4gymzogr/iot_project2024/Pictures/1_5_9dfddd3d-20bd-4d54-b8c2-3854cab92070.png

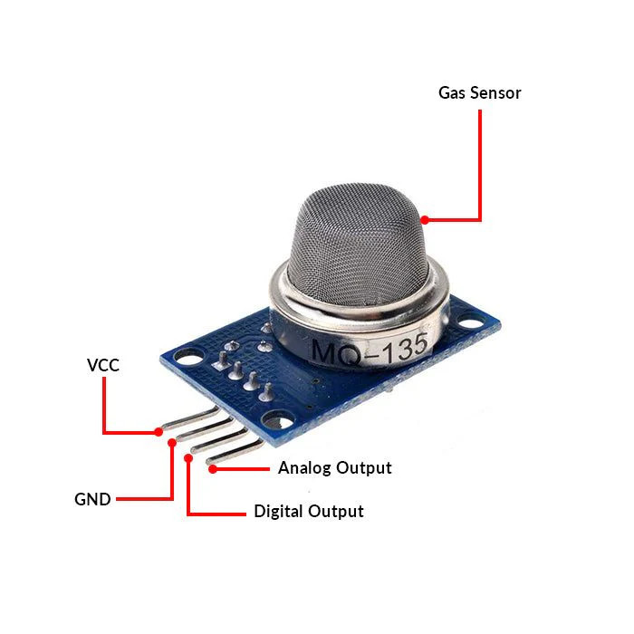
Pictures/1_5_9dfddd3d-20bd-4d54-b8c2-3854cab92070.png
