4gymzogr/iot_project2024/Pictures/1442273400_1452102046.jpg

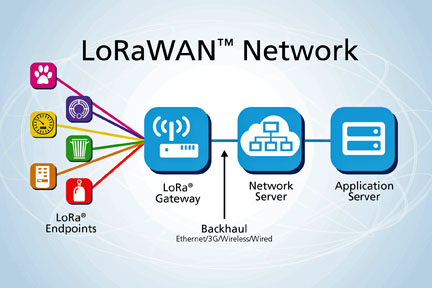
Pictures/1442273400_1452102046.jpg
