4gymzogr/iot_project2024/Pictures/arduino-uno-rev4-minima-dime.jpg

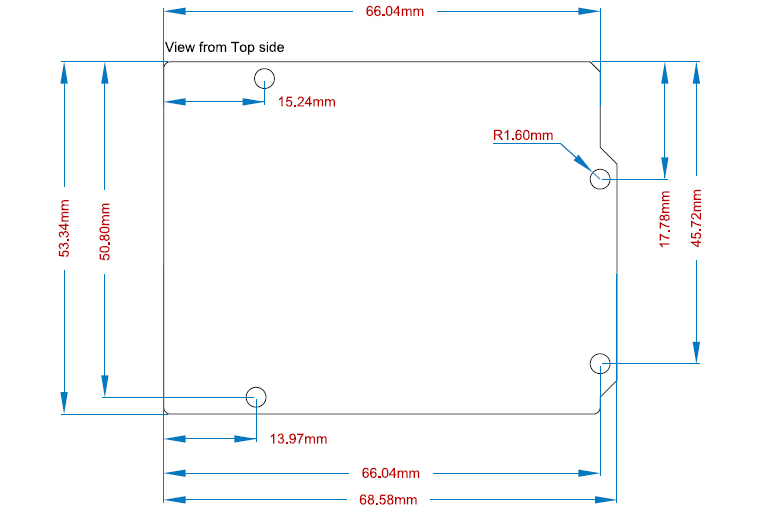
Pictures/arduino-uno-rev4-minima-dime.jpg
