4gymzogr/iot_project2024/Pictures/arduino_mega.png

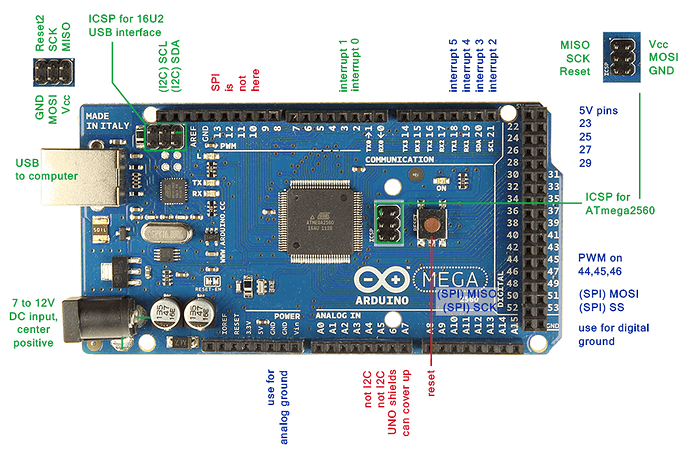
Pictures/arduino_mega.png
