4gymzogr/iot_project2024/Pictures/arduino_ubo.jpg

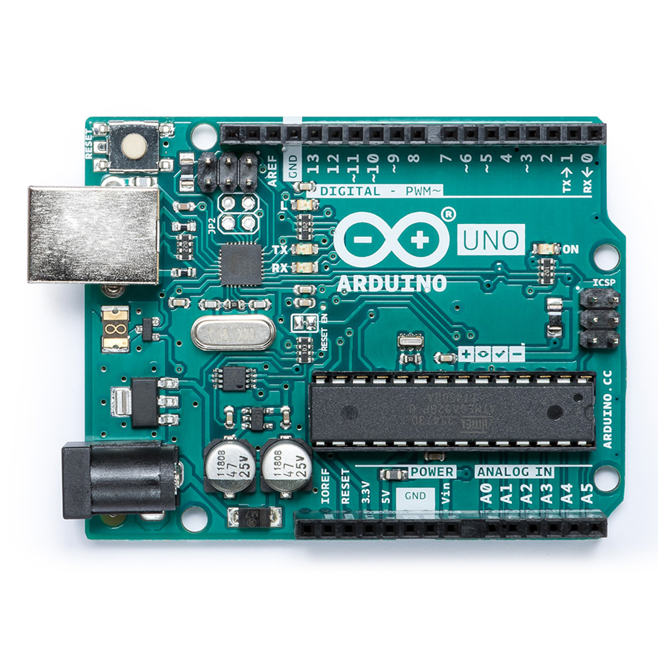
Pictures/arduino_ubo.jpg
