4gymzogr/iot_project2024/Pictures/BME688-Environmental-Sensor-with-Arduino-SPI-Connections.jpg

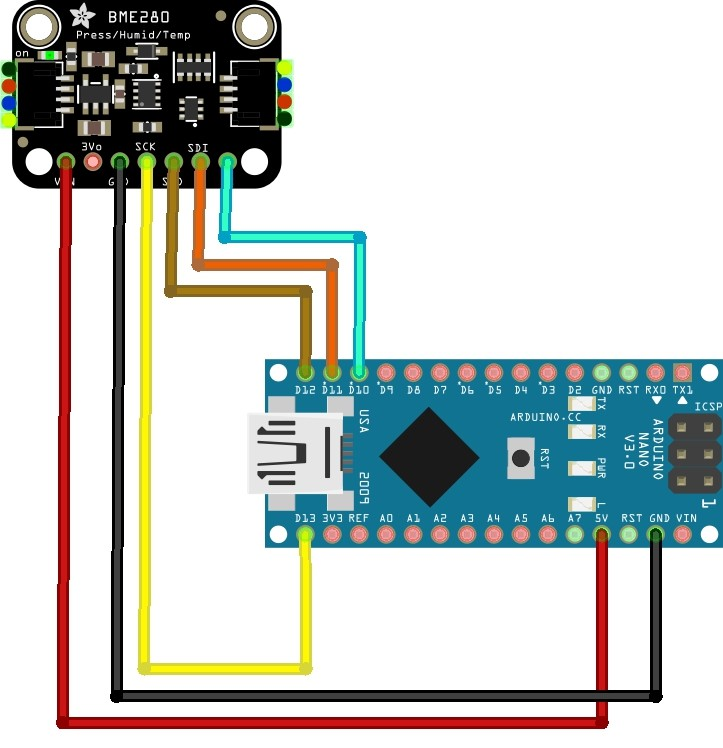
Pictures/BME688-Environmental-Sensor-with-Arduino-SPI-Connections.jpg
