4gymzogr/iot_project2024/Pictures/BME688-Temperature-Humidity-Pressure-and-Gas-Sensor-with-Arduino.jpg

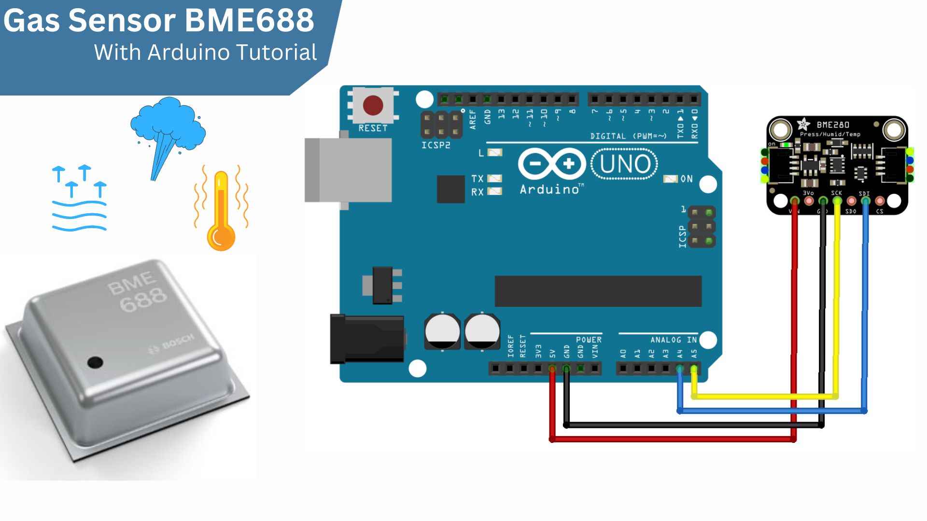
Pictures/BME688-Temperature-Humidity-Pressure-and-Gas-Sensor-with-Arduino.jpg
