4gymzogr/iot_project2024/Pictures/bme688.jpg

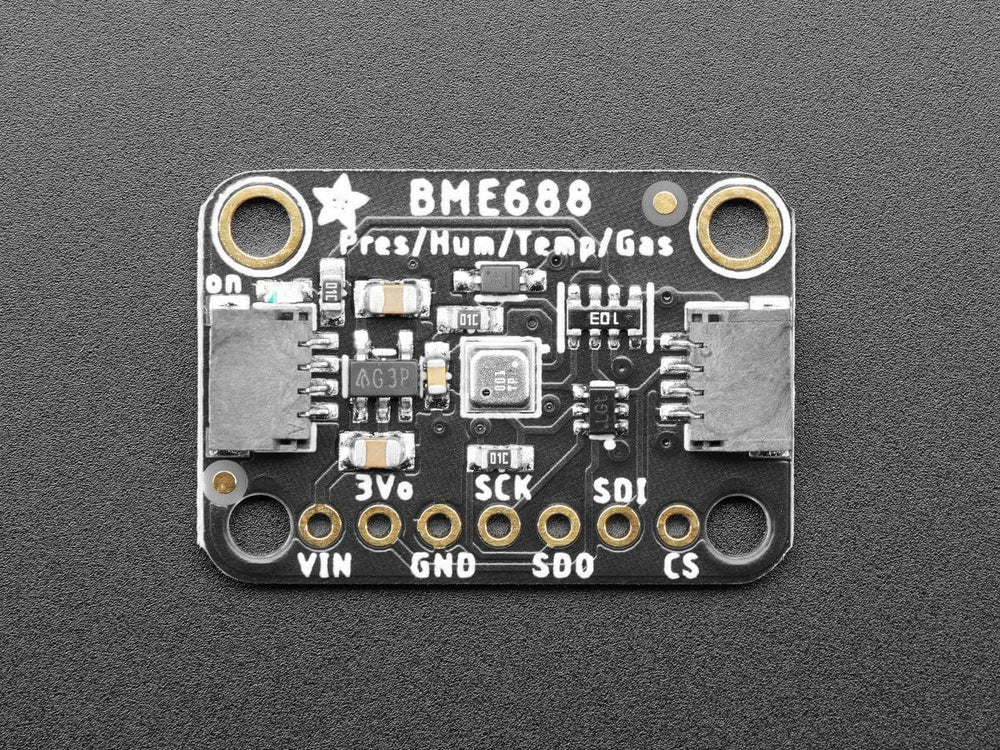
Pictures/bme688.jpg
