4gymzogr/iot_project2024/Pictures/indoor air quality.jpg

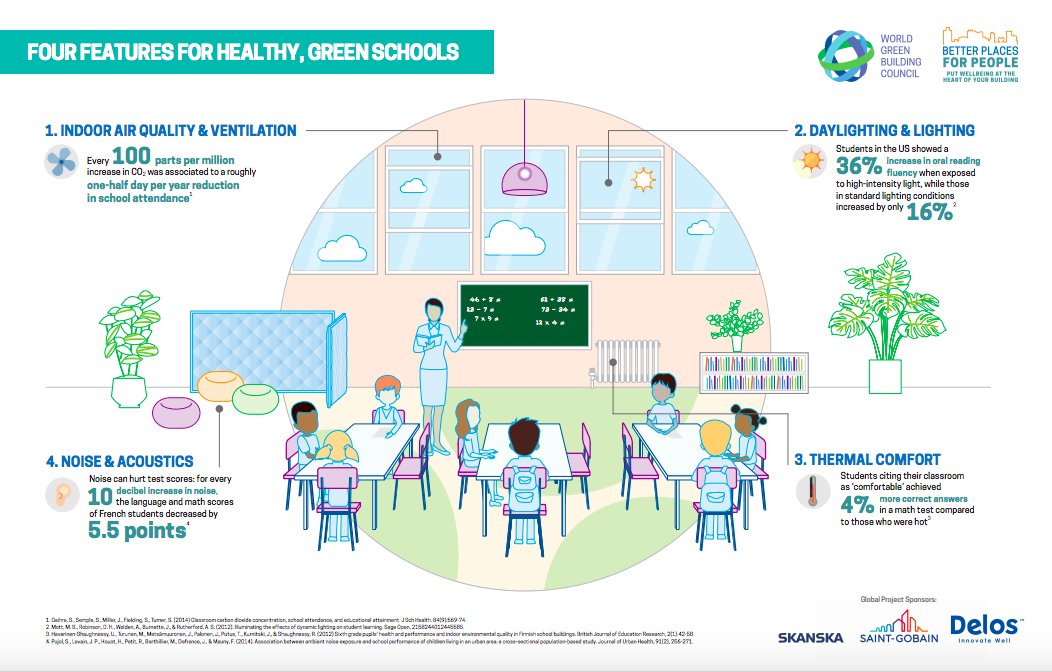
Pictures/indoor air quality.jpg
