4gymzogr/iot_project2024/Pictures/IoT1.png

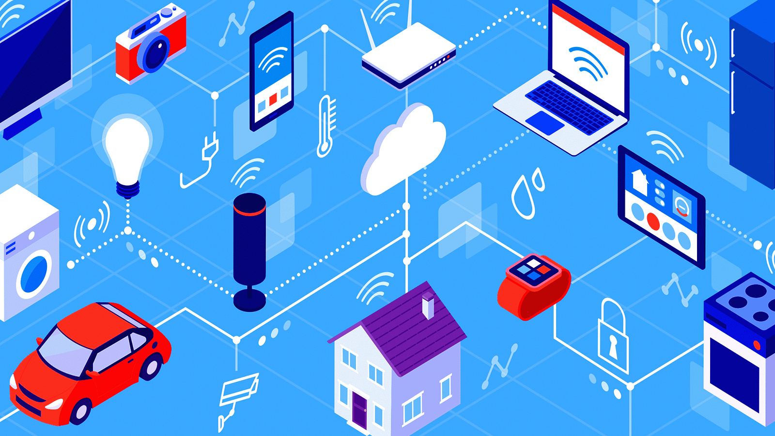
Pictures/IoT1.png
