4gymzogr/iot_project2024/Pictures/IoT2.jpg

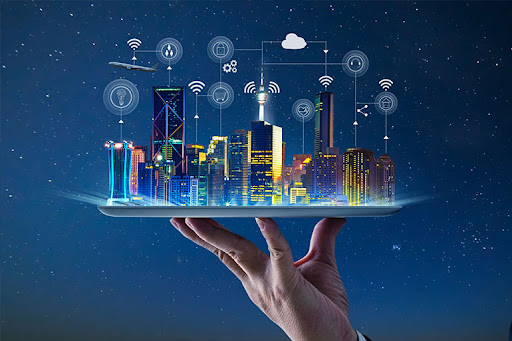
Pictures/IoT2.jpg
