4gymzogr/iot_project2024/Pictures/IoT3.png

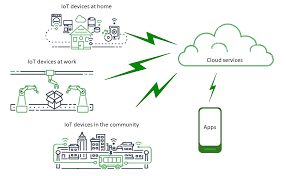
Pictures/IoT3.png
