4gymzogr/iot_project2024/Pictures/IoT4.jpg

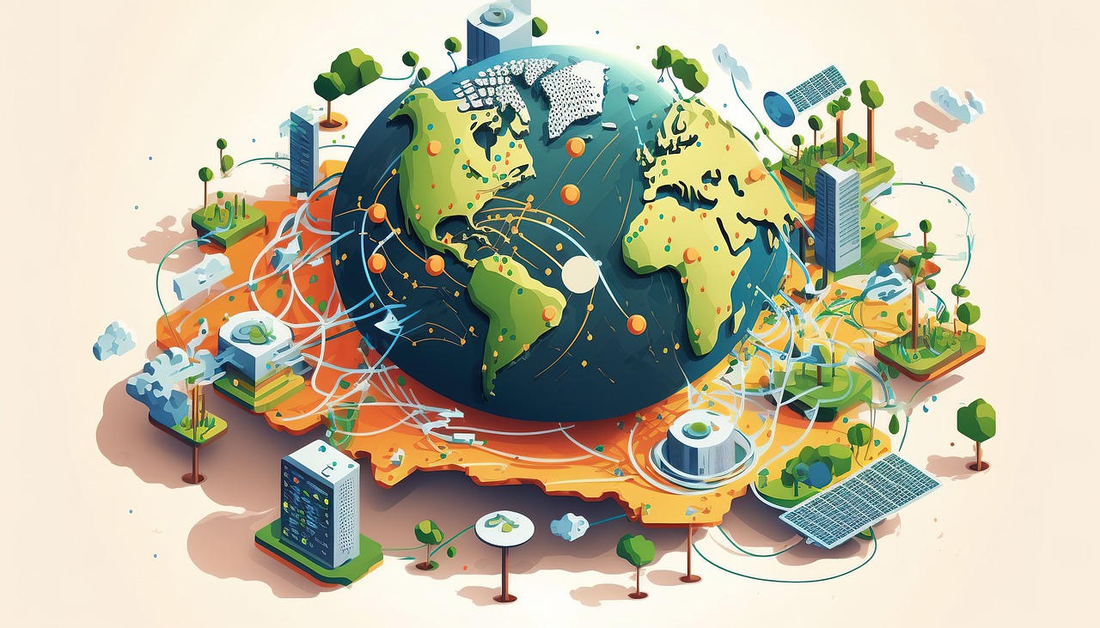
Pictures/IoT4.jpg
