4gymzogr/iot_project2024/Pictures/LDR-wire.jpg

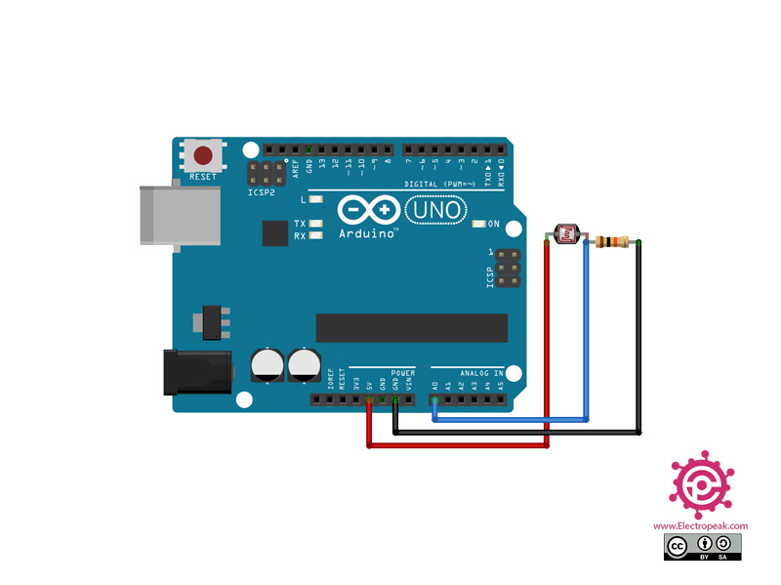
Pictures/LDR-wire.jpg
