4gymzogr/iot_project2024/Pictures/LDR-wire.png

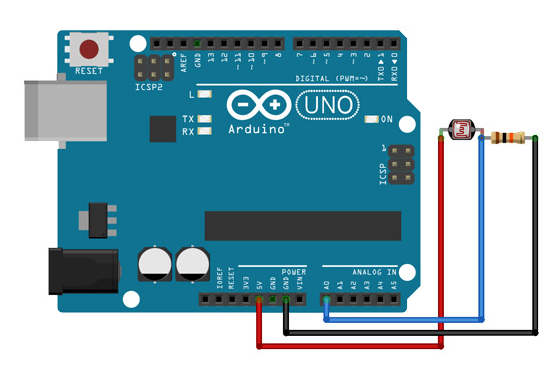
Pictures/LDR-wire.png
