4gymzogr/iot_project2024/Pictures/LDRsensor.jpg

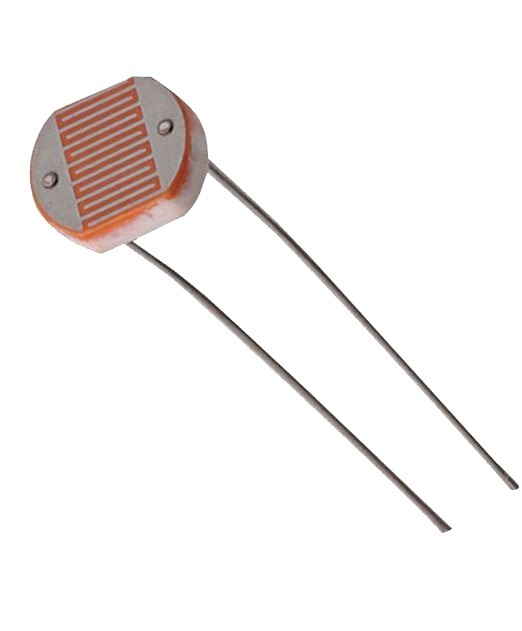
Pictures/LDRsensor.jpg
