4gymzogr/iot_project2024/Pictures/LoRa1.png

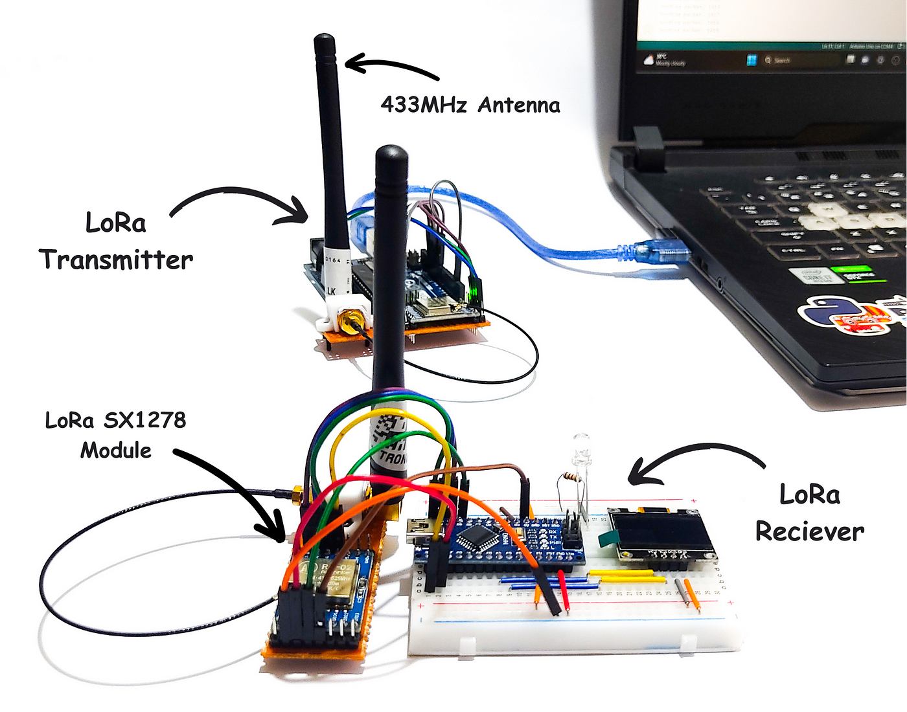
Pictures/LoRa1.png
