4gymzogr/iot_project2024/Pictures/lora-gateway-diagram.png

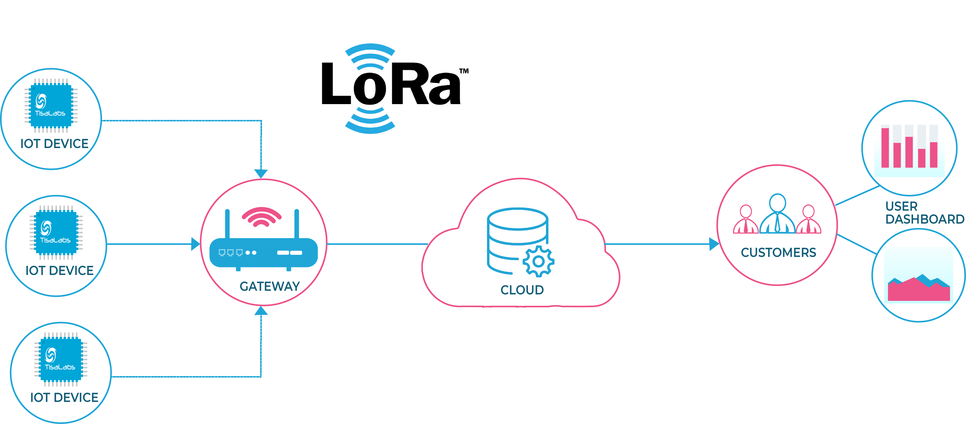
Pictures/lora-gateway-diagram.png
