4gymzogr/iot_project2024/Pictures/LoRa-rfm95w-868s2-3.jpeg

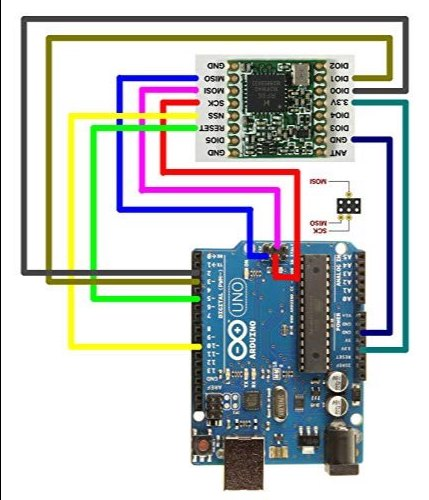
Pictures/LoRa-rfm95w-868s2-3.jpeg
