4gymzogr/iot_project2024/Pictures/LoRa-SX1278-with-Arduino-Nano.png.png

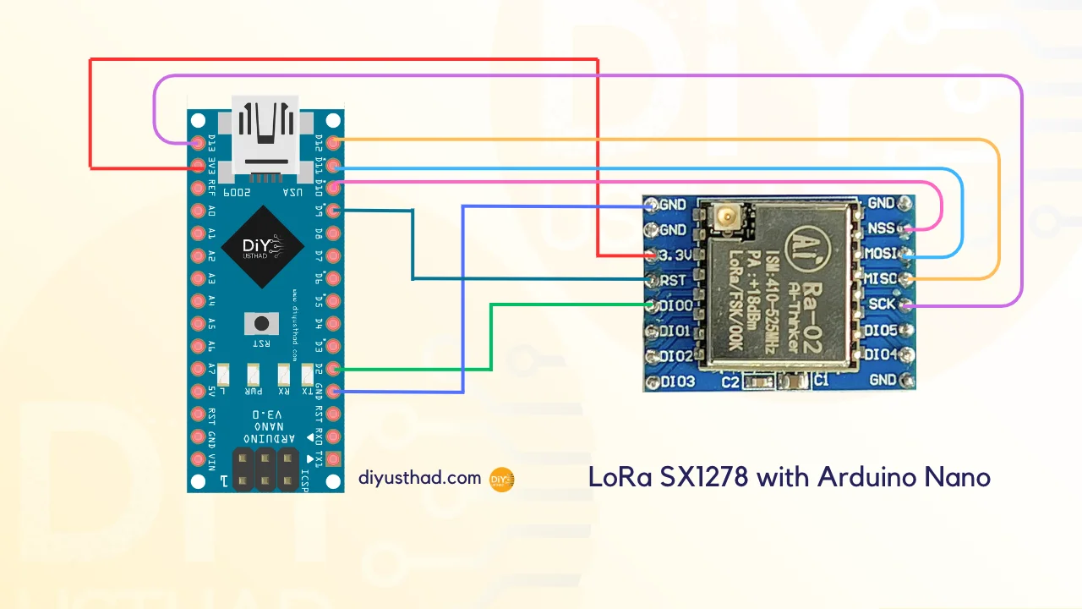
Pictures/LoRa-SX1278-with-Arduino-Nano.png.png
