4gymzogr/iot_project2024/Pictures/LoRa.jpg

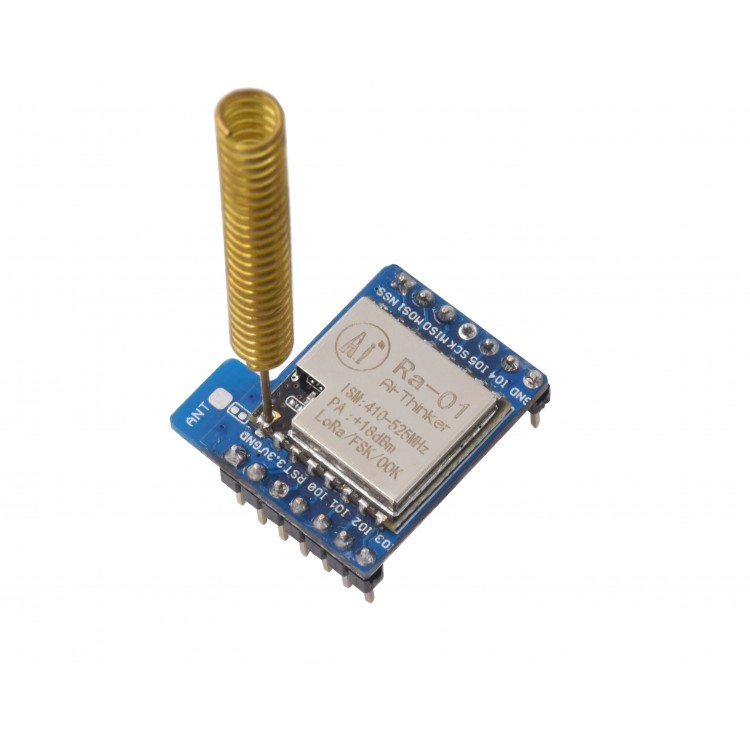
Pictures/LoRa.jpg
