4gymzogr/iot_project2024/Pictures/LoRaInArduinoUNO.jpg

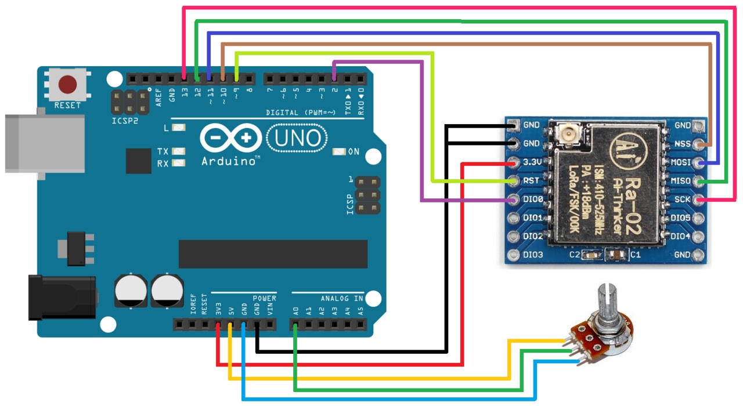
Pictures/LoRaInArduinoUNO.jpg
