4gymzogr/iot_project2024/Pictures/LoRaMQTTNetwork.jpg

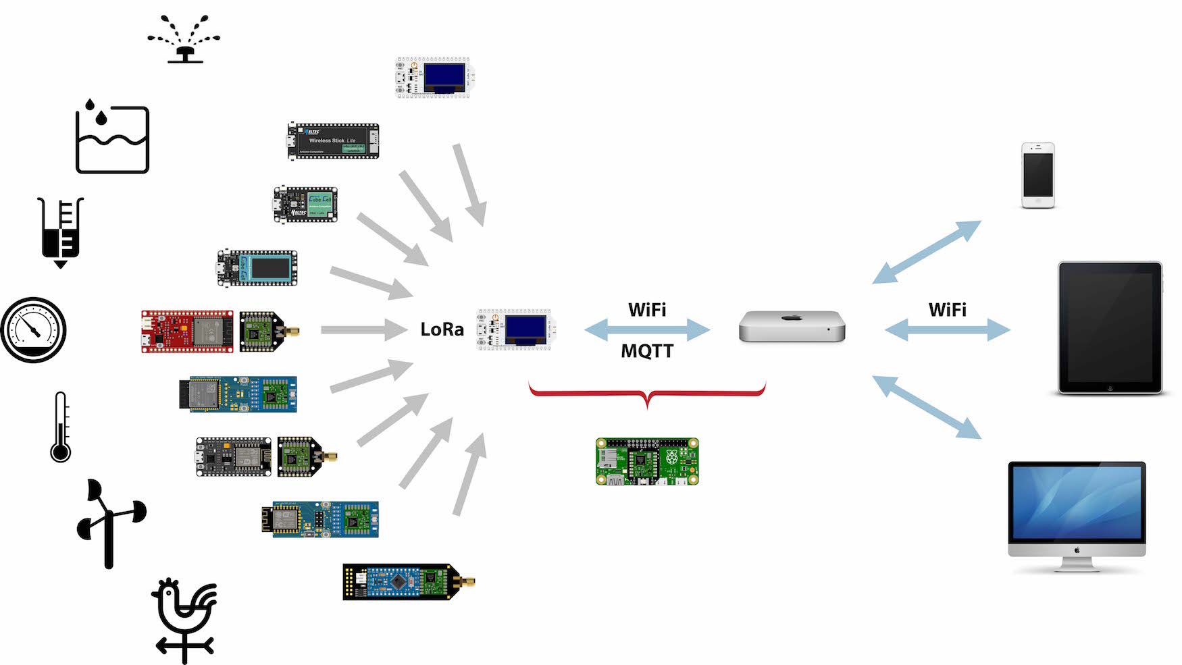
Pictures/LoRaMQTTNetwork.jpg
