4gymzogr/iot_project2024/Pictures/LoRaWAN-Network-Architecture.png

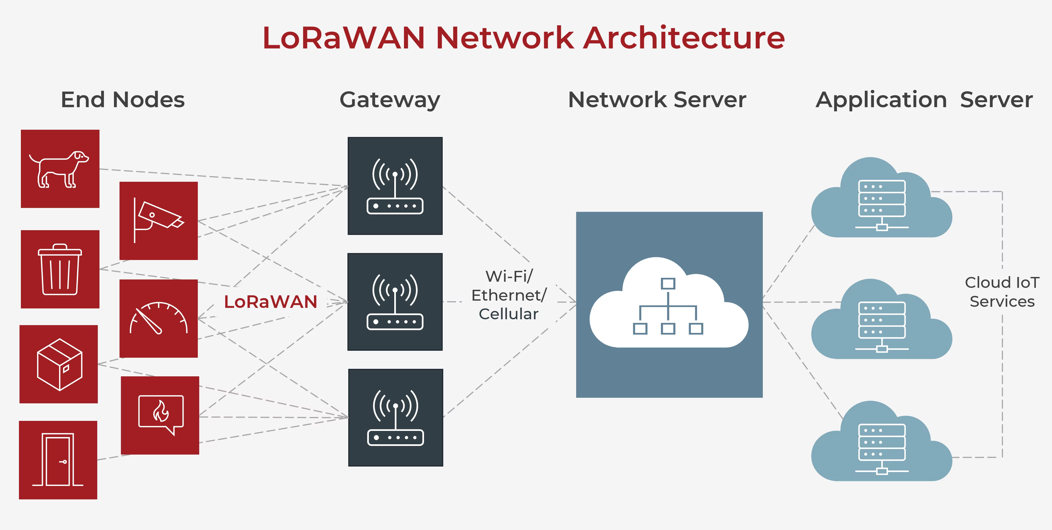
Pictures/LoRaWAN-Network-Architecture.png
