4gymzogr/iot_project2024/Pictures/MQ135-Load-Resistor-Location.png

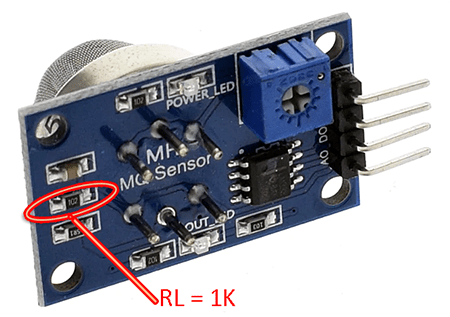
Pictures/MQ135-Load-Resistor-Location.png
