4gymzogr/iot_project2024/Pictures/MQ135.jpeg

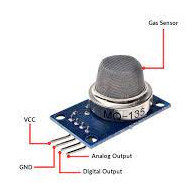
Pictures/MQ135.jpeg
