4gymzogr/iot_project2024/Pictures/MQ135_connect_with_arduino.jpeg

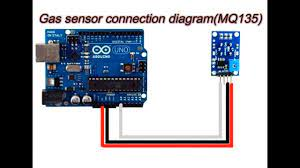
Pictures/MQ135_connect_with_arduino.jpeg
