4gymzogr/iot_project2024/Pictures/mqtt1.png

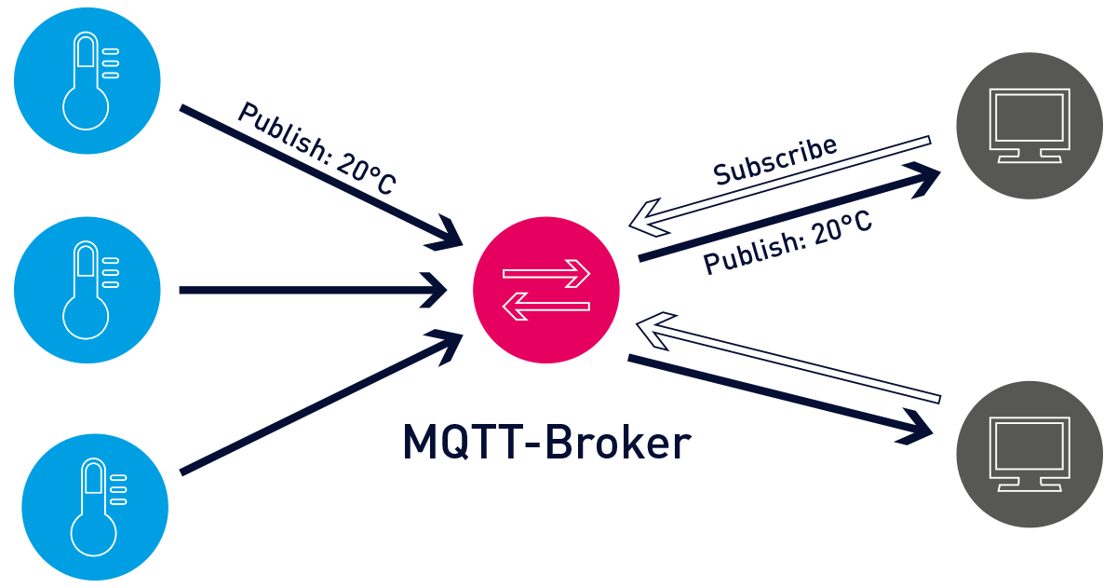
Pictures/mqtt1.png
