4gymzogr/iot_project2024/Pictures/MQTT2.jpg

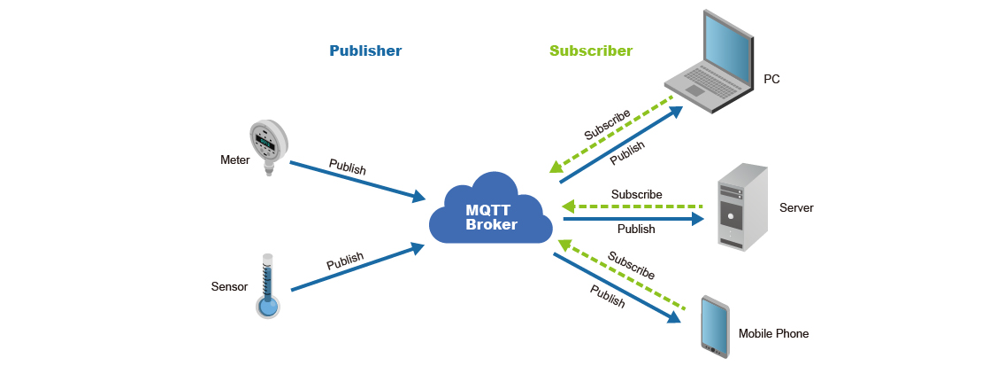
Pictures/MQTT2.jpg
