4gymzogr/iot_project2024/Pictures/OutlineDimensionsArduinoUNORev4WiFi.webp

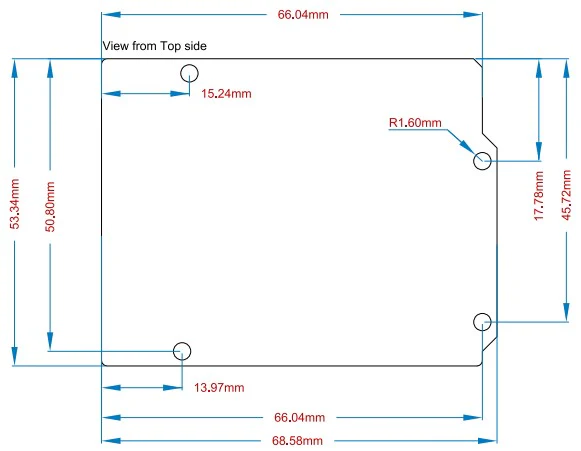
Pictures/OutlineDimensionsArduinoUNORev4WiFi.webp
