4gymzogr/iot_project2024/Pictures/rf001-rfm95w-868s2-2-1000x1000.jpeg

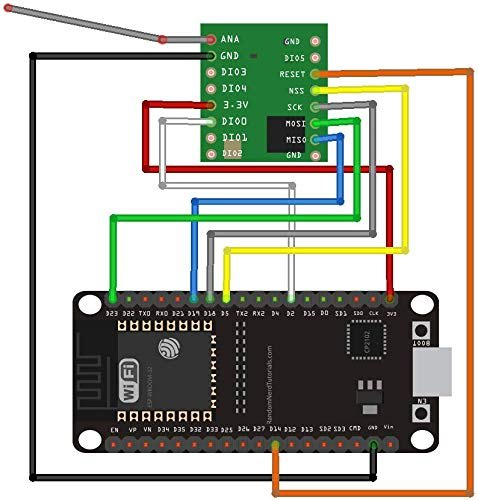
Pictures/rf001-rfm95w-868s2-2-1000x1000.jpeg
