4gymzogr/iot_project2024/Pictures/RoboticsTeamPhotos/IMG_20240421_123717820_HDR.jpg

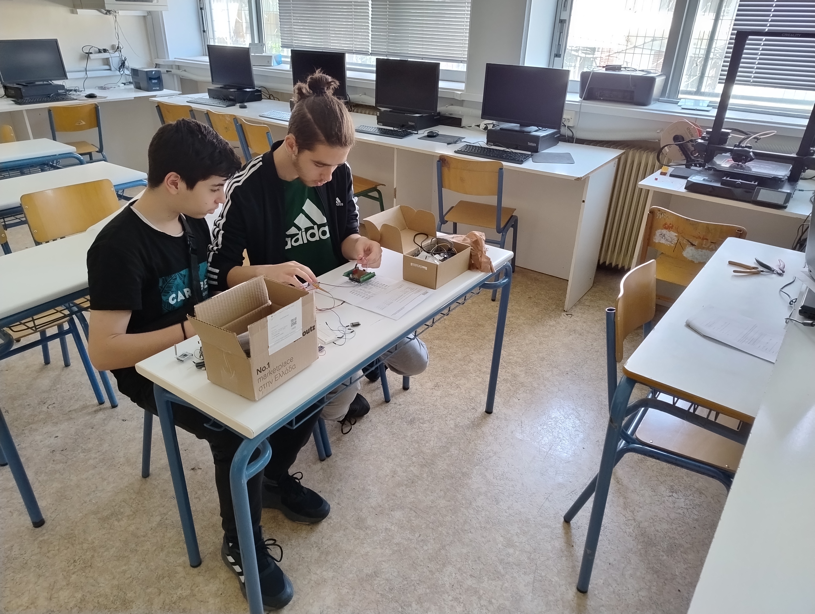
Pictures/RoboticsTeamPhotos/IMG_20240421_123717820_HDR.jpg
