4gymzogr/iot_project2024/Pictures/RoboticsTeamPhotos/IMG_20240421_123722611.jpg

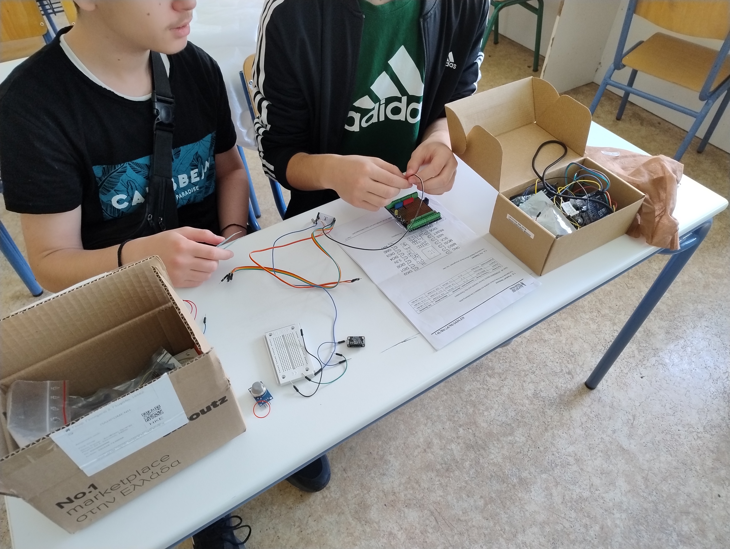
Pictures/RoboticsTeamPhotos/IMG_20240421_123722611.jpg
