4gymzogr/iot_project2024/Pictures/RoboticsTeamPhotos/IMG_20240425_132821488_HDR.jpg

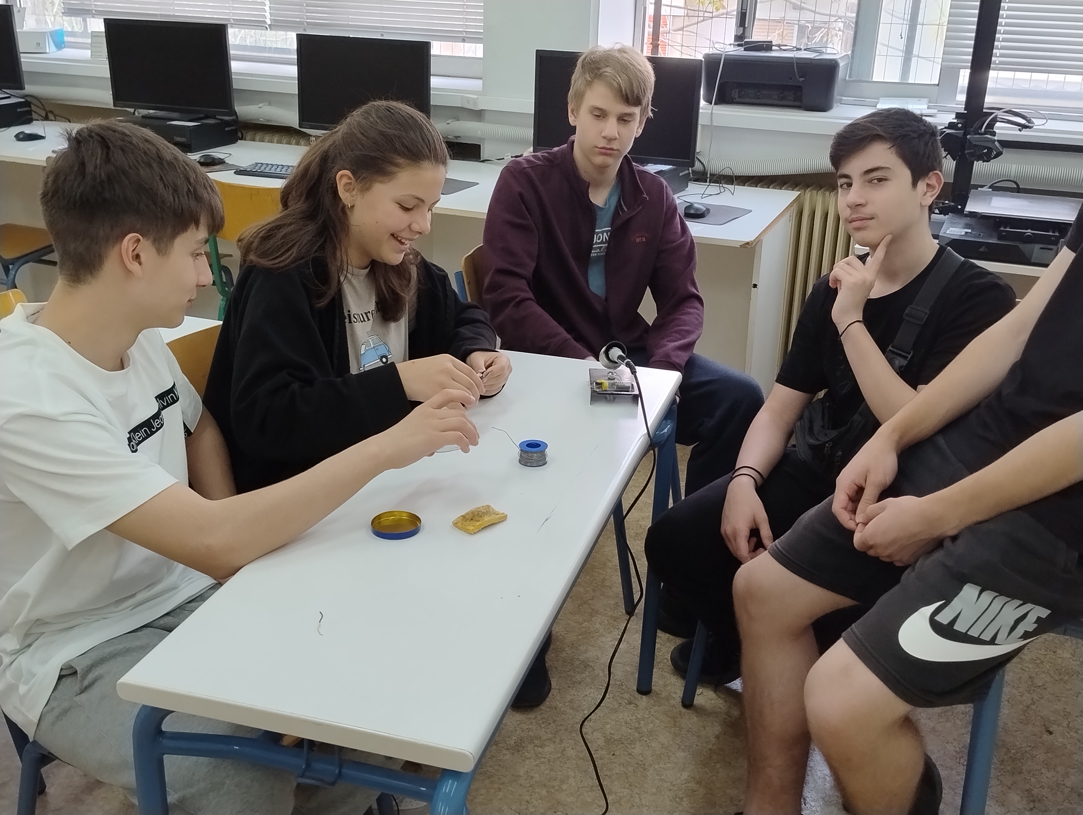
Pictures/RoboticsTeamPhotos/IMG_20240425_132821488_HDR.jpg
