4gymzogr/iot_project2024/Pictures/RoboticsTeamPhotos/IMG_20240425_132825725_HDR.jpg

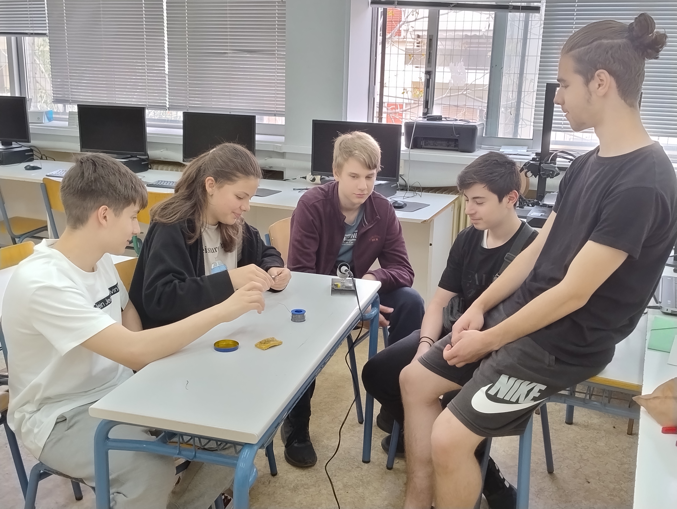
Pictures/RoboticsTeamPhotos/IMG_20240425_132825725_HDR.jpg
