4gymzogr/iot_project2024/Pictures/RoboticsTeamPhotos/IMG_20240425_133020919_HDR.jpg

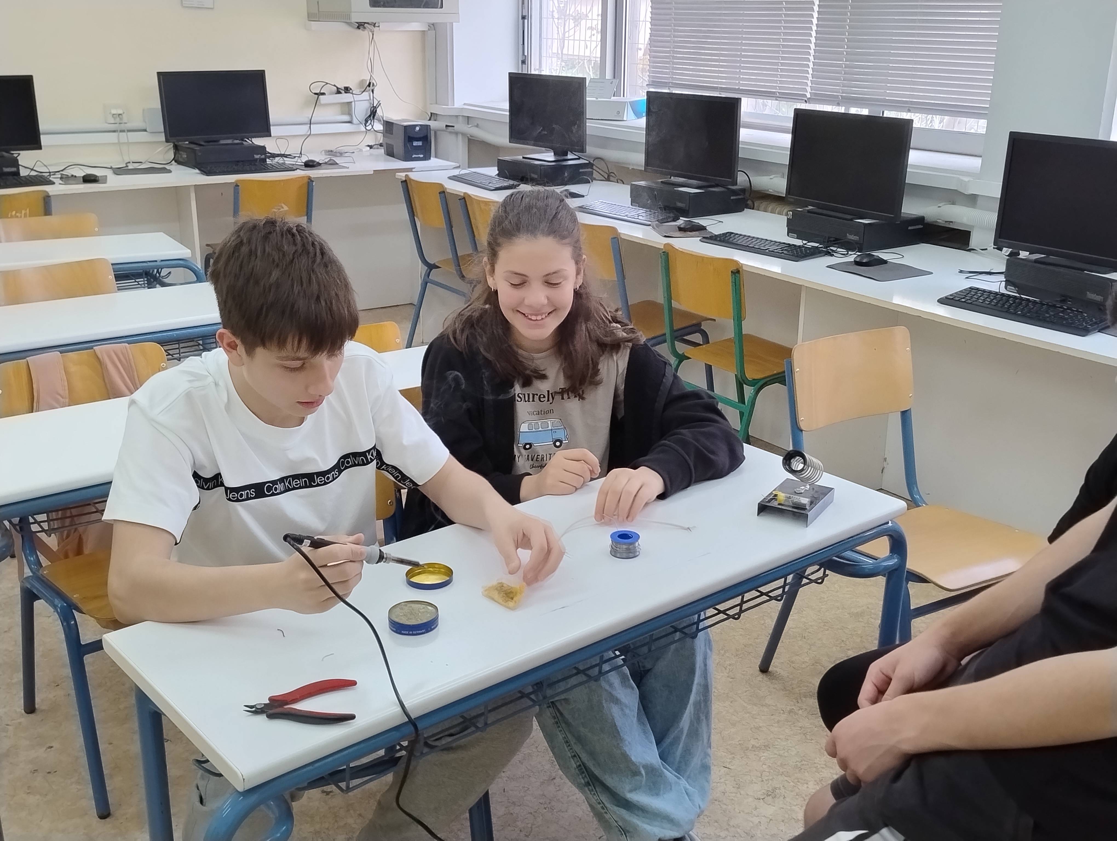
Pictures/RoboticsTeamPhotos/IMG_20240425_133020919_HDR.jpg
