4gymzogr/iot_project2024/Pictures/RoboticsTeamPhotos/IMG_20240430_075011152.jpg

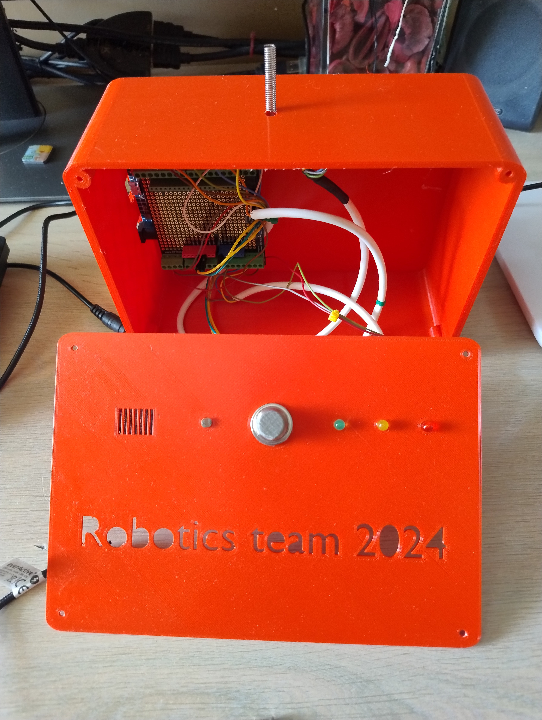
Pictures/RoboticsTeamPhotos/IMG_20240430_075011152.jpg
