4gymzogr/iot_project2024/Pictures/RoboticsTeamPhotos/IMG_20240430_075111997.jpg

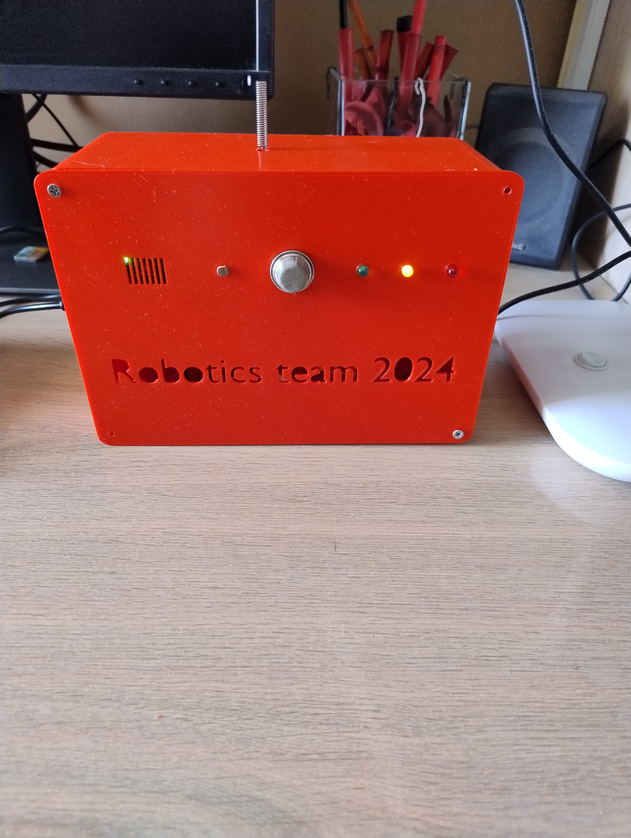
Pictures/RoboticsTeamPhotos/IMG_20240430_075111997.jpg
