4gymzogr/iot_project2024/Pictures/BME688_Arduino_wiring_UNO.jpg

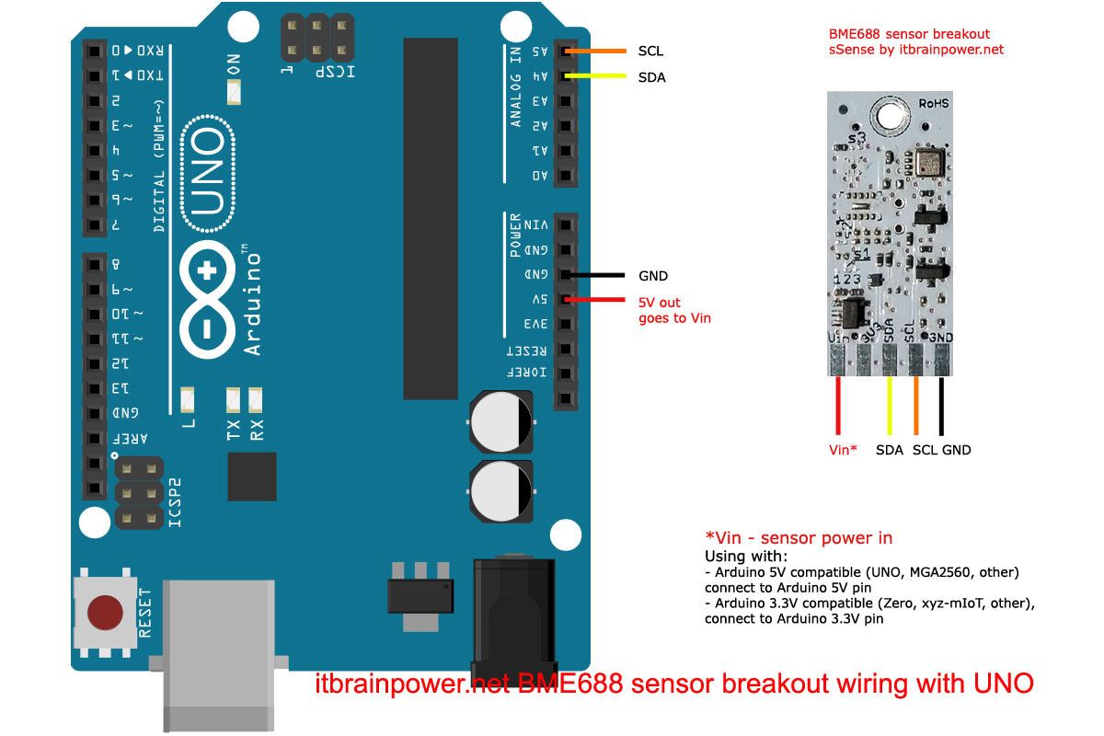
Pictures/BME688_Arduino_wiring_UNO.jpg
