4gymzogr/iot_project2024/Pictures/RoboticsTeamPhotos/IMG_20240430_074945481.jpg

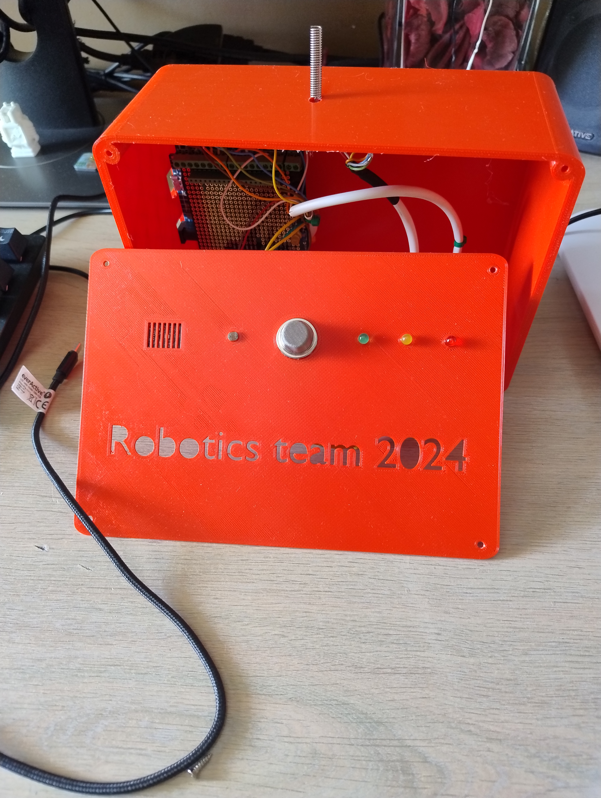
Pictures/RoboticsTeamPhotos/IMG_20240430_074945481.jpg
