4gymzogr/iot_project2024/Pictures/RoboticsTeamPhotos/IMG_20240430_074959204.jpg

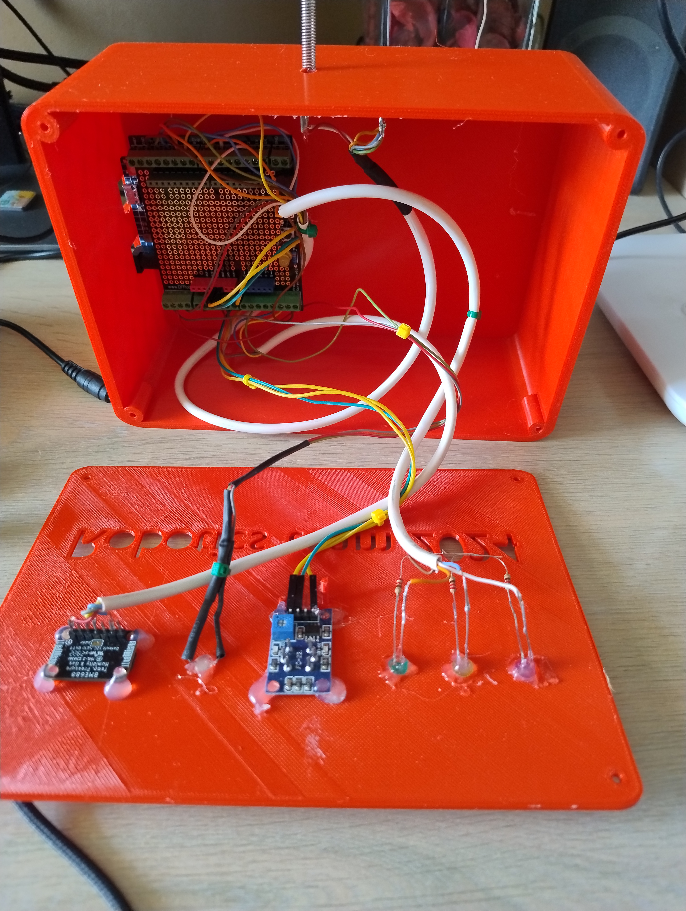
Pictures/RoboticsTeamPhotos/IMG_20240430_074959204.jpg
